ukhov79/NES-gamepads-to-PS2/images/M2_5x6mm.png

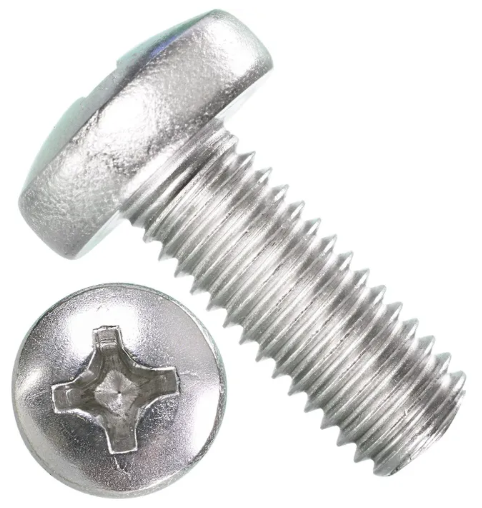
images/M2_5x6mm.png
