ukhov79/NES-gamepads-to-PS2/images/Metal-Button-Switch2.png

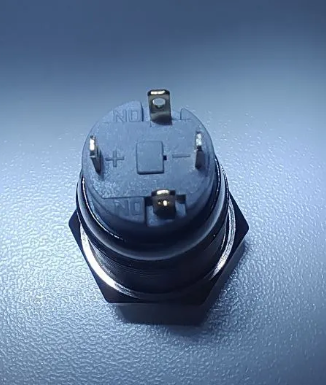
images/Metal-Button-Switch2.png
