ukhov79/NES-gamepads-to-PS2/images/Metal-Button-Switch.png

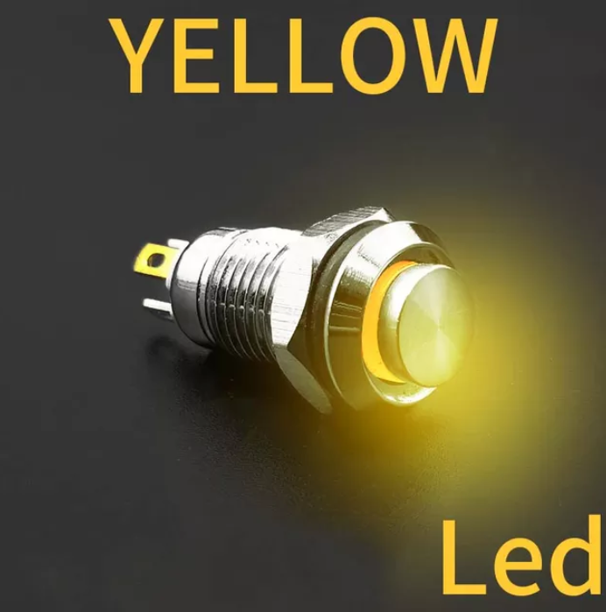
images/Metal-Button-Switch.png
