ukhov79/NES-gamepads-to-PS2/images/PC2-MDC-S2.png

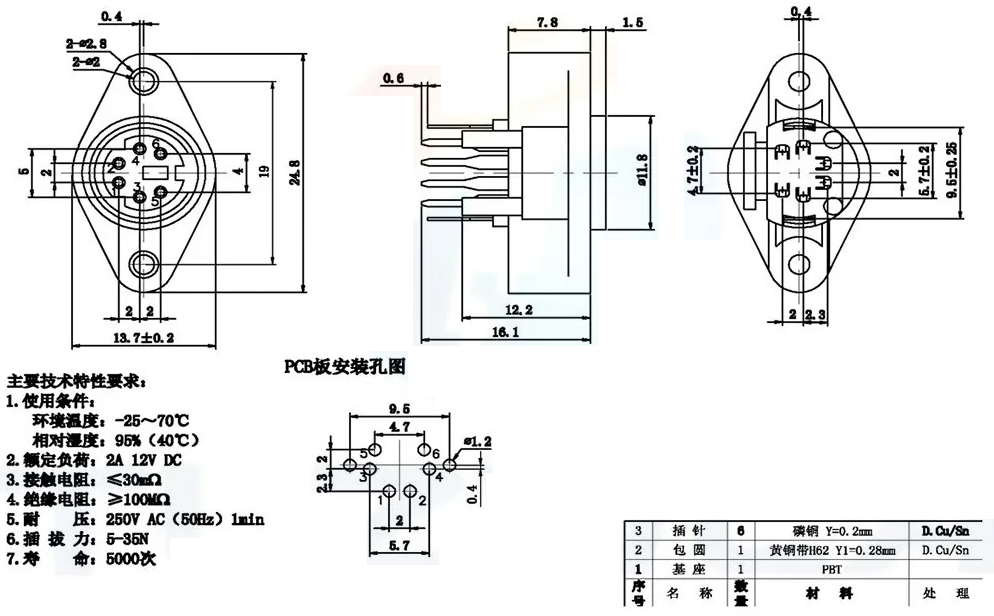
images/PC2-MDC-S2.png
