ukhov79/NES-gamepads-to-PS2/images/Sega-slot.png

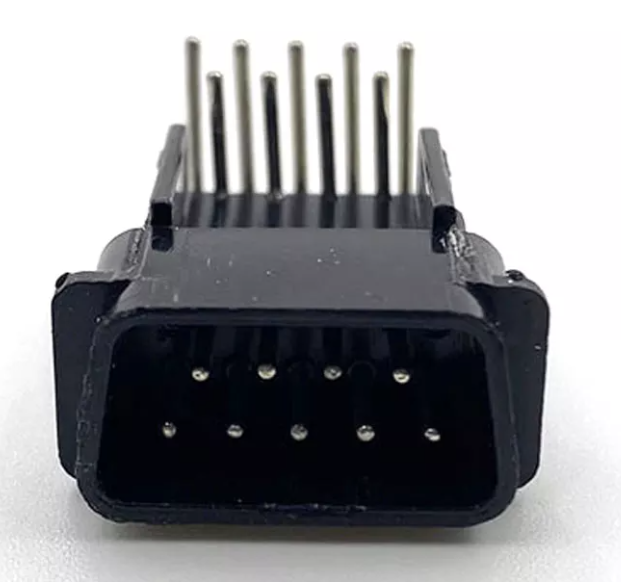
images/Sega-slot.png
